esynr3z/nixie-ps/ltspice/nixie-ps.asc

Cc: cap; 22nF
Cin: cap; 100µF
Cout: cap; 0.47µF
Csn: cap; 0.01µF
D1: diode; ES3J
D2: TVSdiode; SMDJ70CA
Lp: ind2; {Lp}
Ls: ind2; {Ls}
M1: nmos; irfh7185pbf
Rc: res; 4.7k
Rfa: res; 47k
Rfb1: res; {Rfb1}
Rfb2: res; {Rfb2}
Rload: res; 9.4k
Rsn: res; 0.033
Rtrim: res; {Rtrim}
U1: LM3488_TRANS
Vcc: voltage; 5; Rser=0.1
Named nets: 0, Vout, Vd, Vg, Vin, Vfb
.tran 0 10m 1u 1u uic
.include ES3J.lib
K Lp Ls 0.95
.include irfh7185pbf.spi
.include SMDJxxxCA.lib
.param Vout = {180} Vfb = {1.22}
.param Rfb1 = {1.2Meg} Rfb2 = {7.5k}
.param Rtrim = {(Vfb*Rfb1)/(Vout-Vfb)-Rfb2}
.meas Rtrim__ param Rtrim
180V 20mA @ 5V in
180V 40mA @ 12V in
.param Al = {100nH} Wp = {10} Ws = {145}
.param Lp = {Wp * Wp * Al} Ls = {Ws * Ws * Al}
.meas Lp__ param Lp
.meas Ls__ param Ls
